freeDSP/freeDSP-INFINITAS/SOURCES/XMOS/app_usb_aud_xk_216_mc/src/extensions/infinitas.h

/*
 * infinitas.h
 *
 *  Created on: 04.10.2018
 *      Author: rkn
 */

#ifndef INFINITAS_H_
#define INFINITAS_H_

#define I2C_ADDR_EXPANSION1 (0xE4)
#define I2C_ADDR_EXPANSION2 (0xE0)

#define I2C_ADDR_PORT1_BOARD1 (0x08)
#define I2C_ADDR_PORT1_BOARD2 (0x04)
#define I2C_ADDR_PORT1_BOARD3 (0x02)
#define I2C_ADDR_PORT1_BOARD4 (0x01)

#define I2C_ADDR_PORT2_BOARD1 (0x04)
#define I2C_ADDR_PORT2_BOARD2 (0x08)
#define I2C_ADDR_PORT2_BOARD3 (0x01)
#define I2C_ADDR_PORT2_BOARD4 (0x02)

#endif /* INFINITAS_H_ */
