freeDSP/freeDSP-INFINITAS/SOURCES/XMOS/app_usb_aud_xk_216_mc/src/extensions/adau1452.c

/*
 * adau1452.c
 *
 *  Created on: 22.01.2018
 *      Author: rkn
 */

#include <assert.h>
#include "devicedefines.h"
#include <platform.h>
#include "gpio_access.h"
#include "i2c_shared.h"

void adau1452_downloadFirmware( void ) {

}
